Alberyn/Organaizer-for-drill/CAD/Задвижка 5мм.SLDPRT

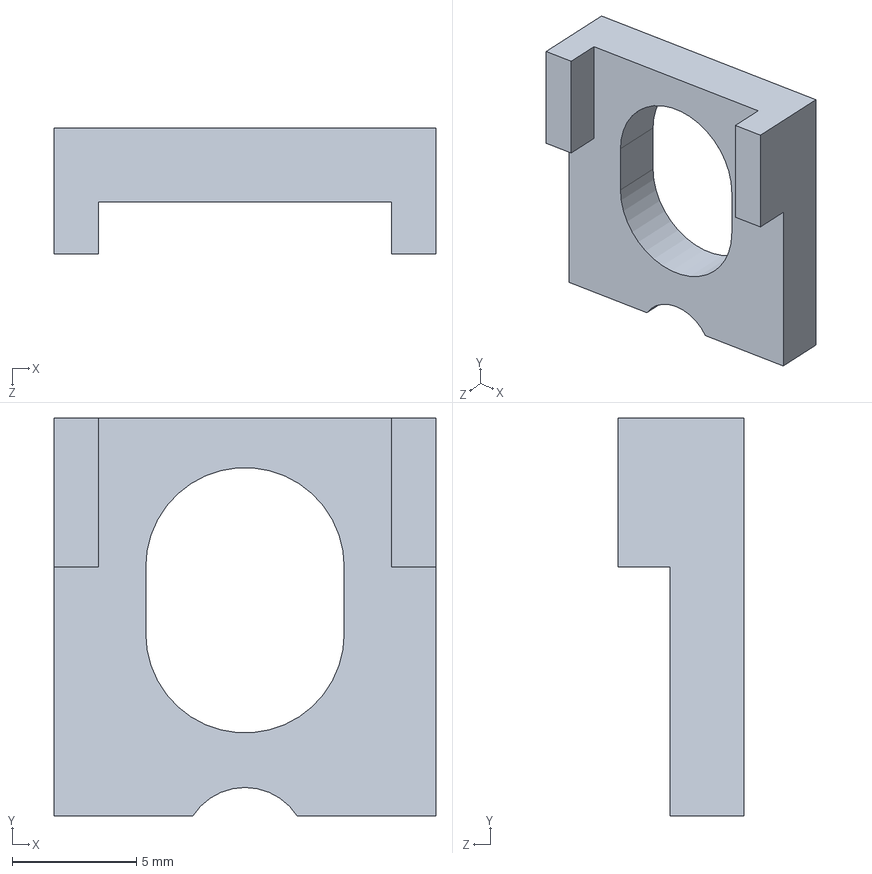
[picture p41: CAD file, 2023-10-13]
CAD/Задвижка 5мм.SLDPRT
15.4 x 16.0 x 5.10 mm
