Alberyn/Organaizer-for-drill/CAD/Задвижка 11мм.SLDPRT

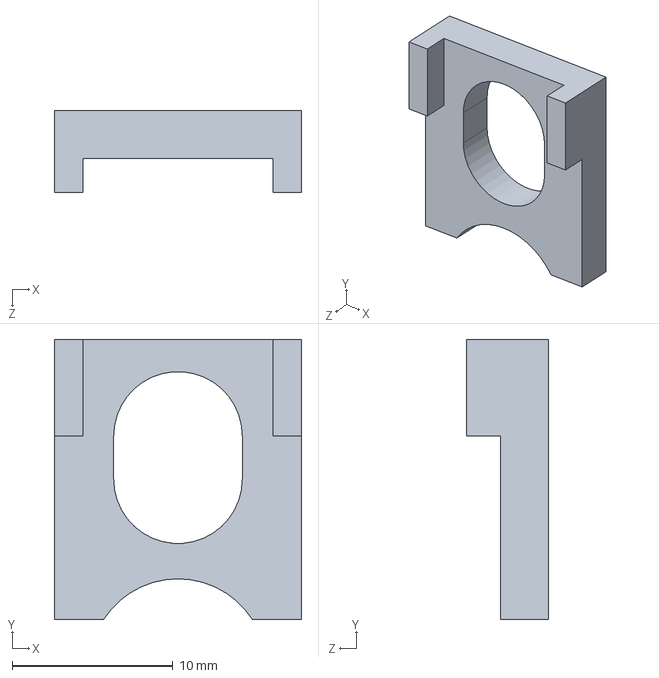
[picture p42: CAD file, 2023-10-13]
CAD/Задвижка 11мм.SLDPRT
15.4 x 17.4 x 5.10 mm
