Alberyn/Organaizer-for-drill/CAD/Поддержка.SLDPRT

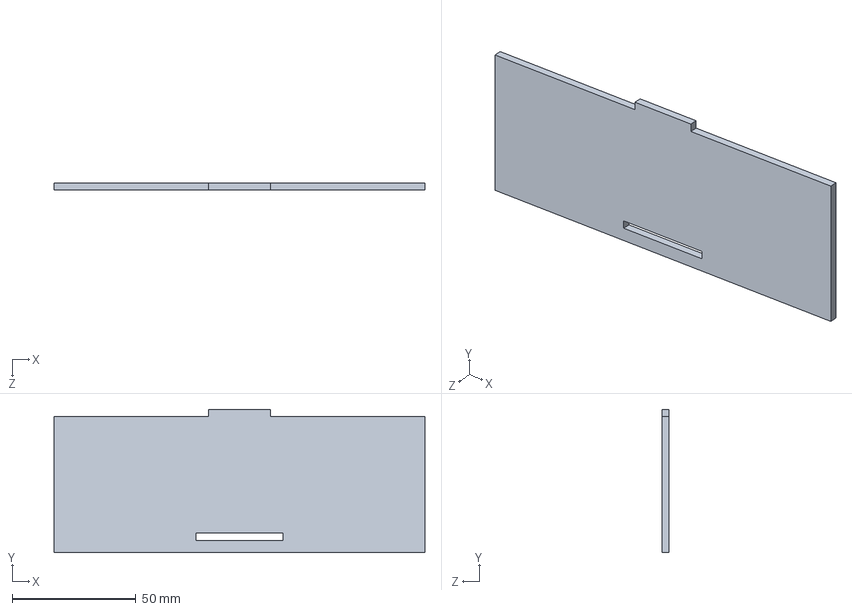
[picture p43: CAD file, 2023-10-13]
CAD/Поддержка.SLDPRT
150.0 x 58.0 x 3.00 mm
