Alberyn/Organaizer-for-drill/CAD/Задняя стенка.SLDPRT

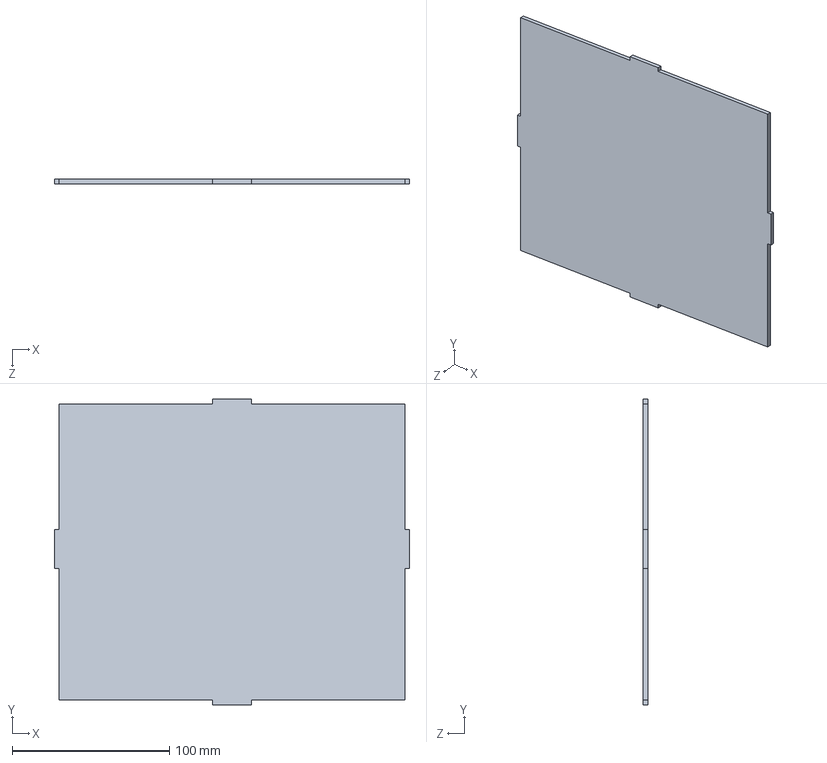
[picture p44: CAD file, 2023-10-13]
CAD/Задняя стенка.SLDPRT
226.0 x 194.7 x 3.00 mm
