Alberyn/Organaizer-for-drill/CAD/Задвижка 3мм.SLDPRT

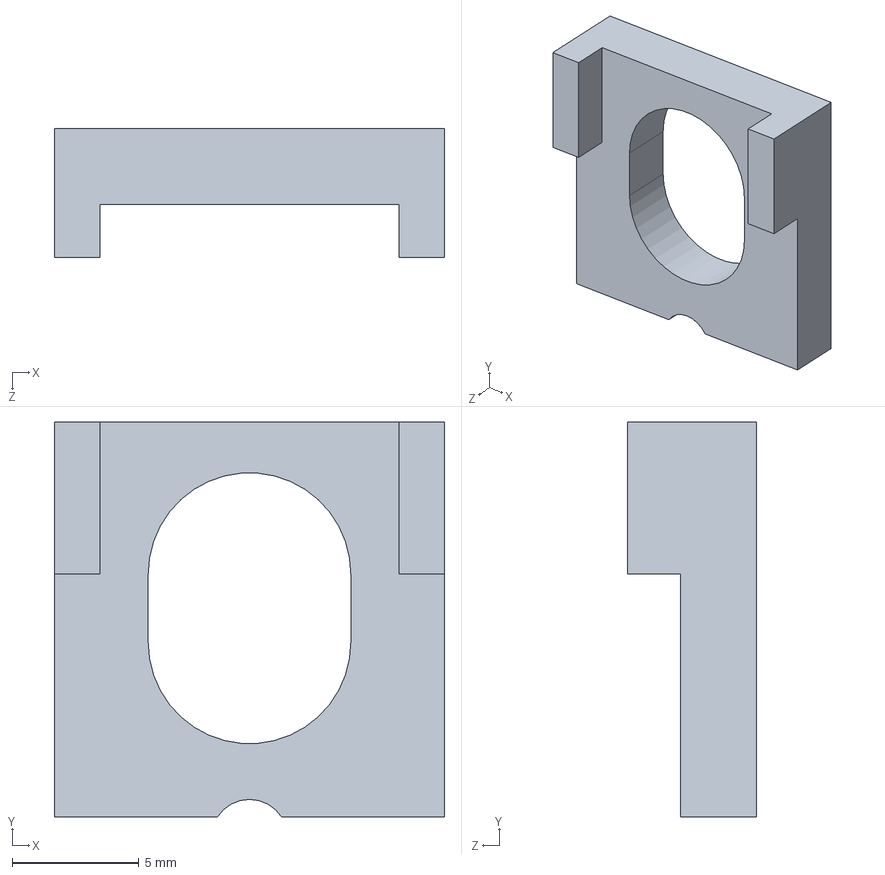
[picture p45: CAD file, 2023-10-13]
CAD/Задвижка 3мм.SLDPRT
15.4 x 15.6 x 5.10 mm
